Ansuzalgiz/SABR/Images/Battery.jpg

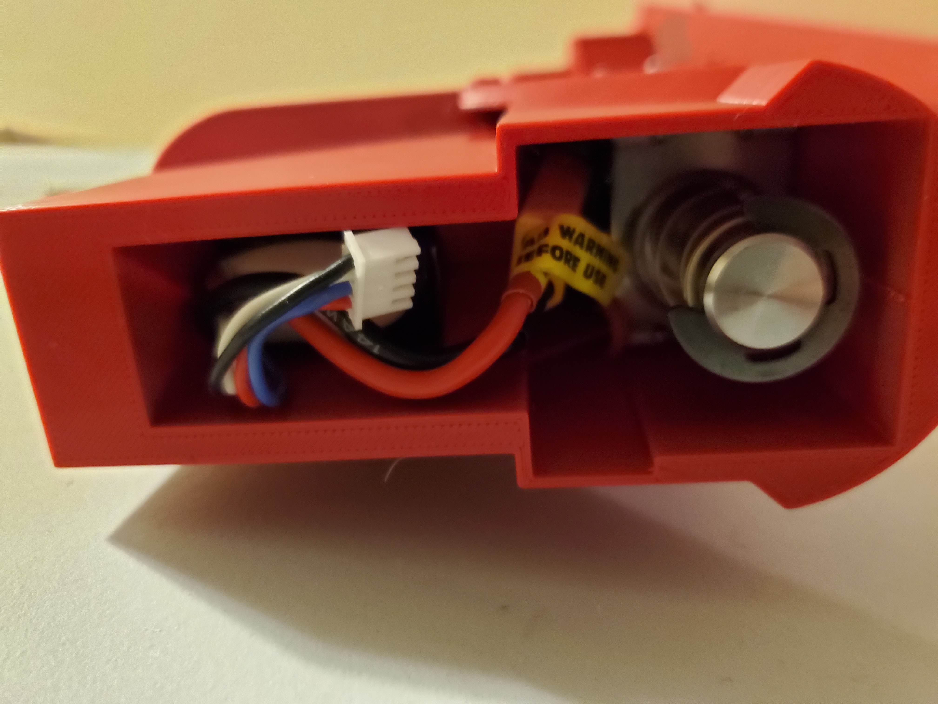
Images/Battery.jpg
