Ansuzalgiz/SABR/Images/Motors.jpg

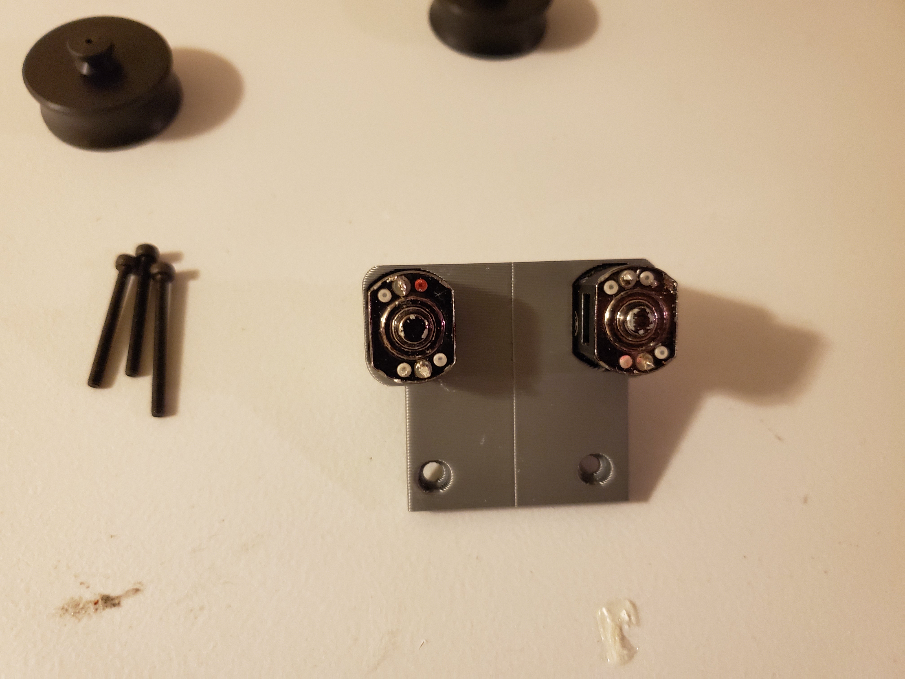
Images/Motors.jpg
