Ansuzalgiz/SABR/Images/ThreadedInserts.jpg

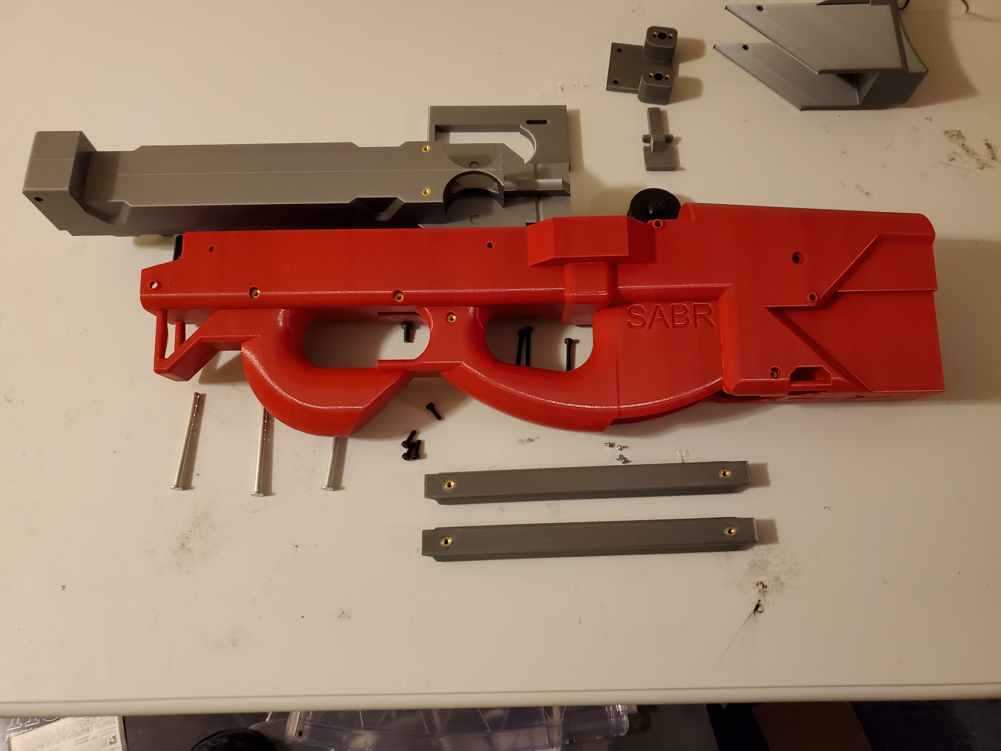
Images/ThreadedInserts.jpg
