Ansuzalgiz/SABR/STL/Barrel.stl

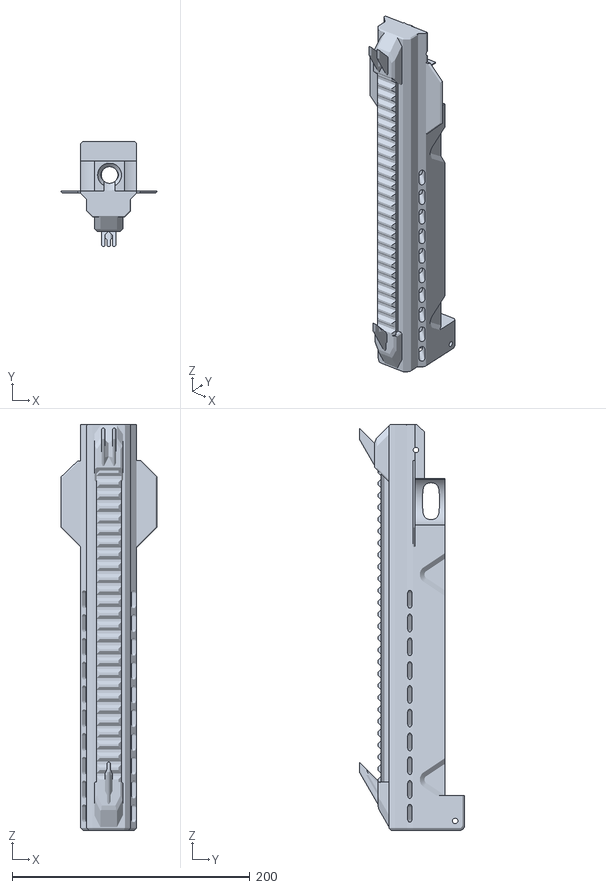
[picture p24: CAD file, 2019-04-15]
STL/Barrel.stl
80.6 x 88.7 x 341.5
