Ansuzalgiz/SABR/STL/130MotorSupport.stl

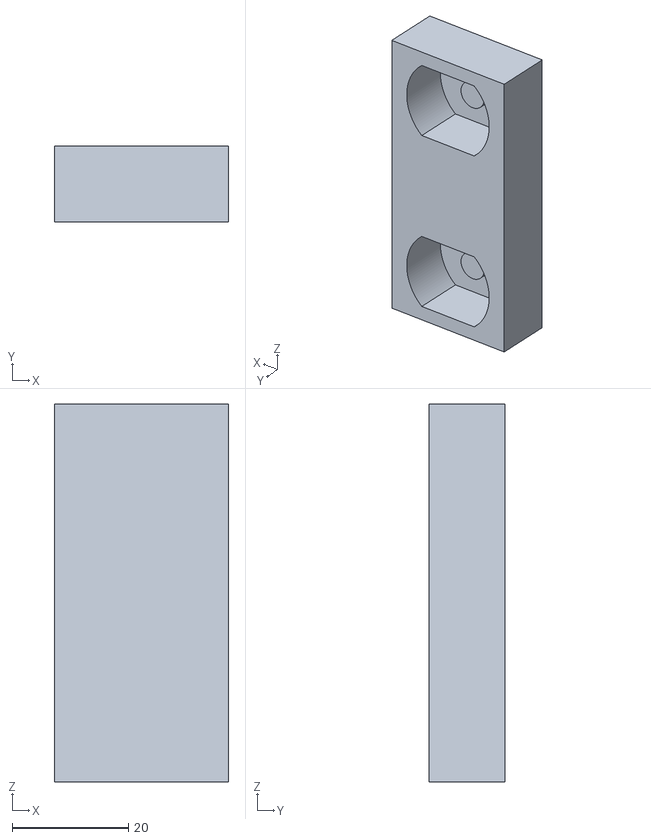
[picture p25: CAD file, 2019-04-15]
STL/130MotorSupport.stl
30.0 x 13.0 x 65.0
