Ansuzalgiz/SABR/STL/Rail.stl

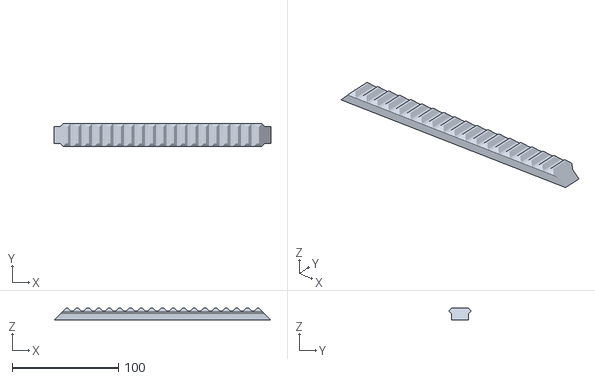
[picture p26: CAD file, 2019-04-15]
STL/Rail.stl
204.0 x 21.2 x 11.3
