Ansuzalgiz/SABR/Images/FlywheelCageInstall.jpg

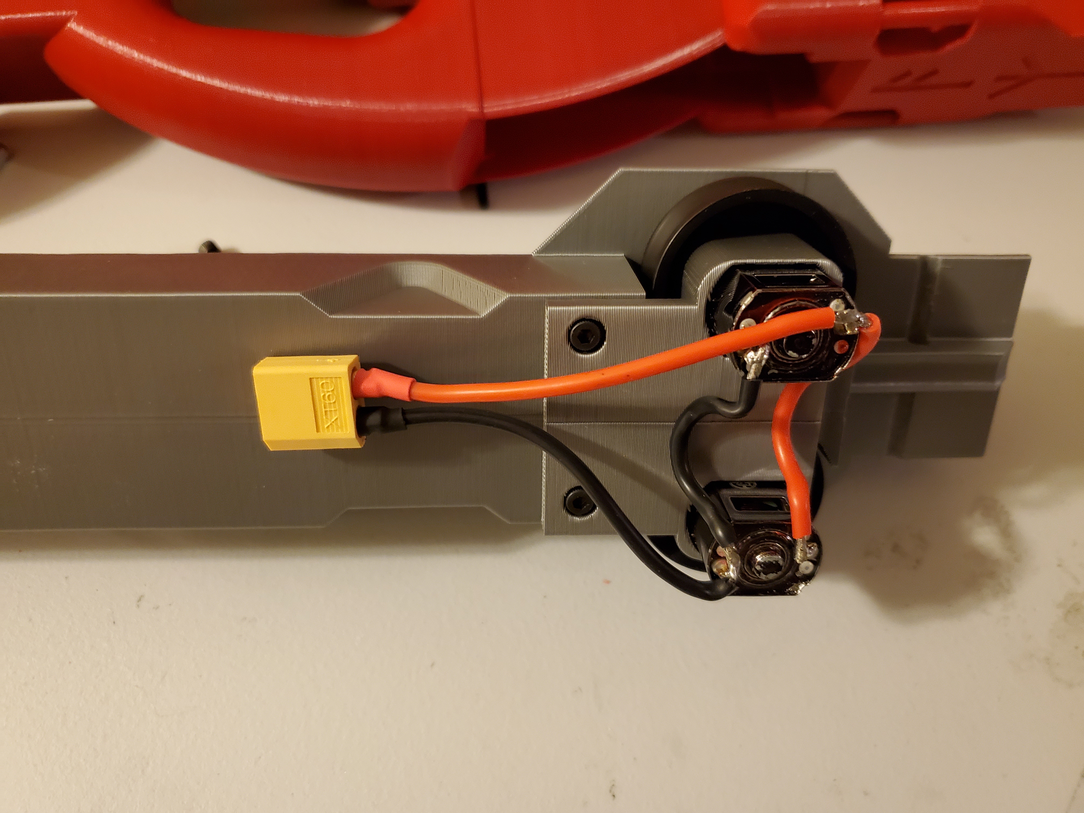
Images/FlywheelCageInstall.jpg
