Ansuzalgiz/SABR/Images/FlywheelInstallation.jpg

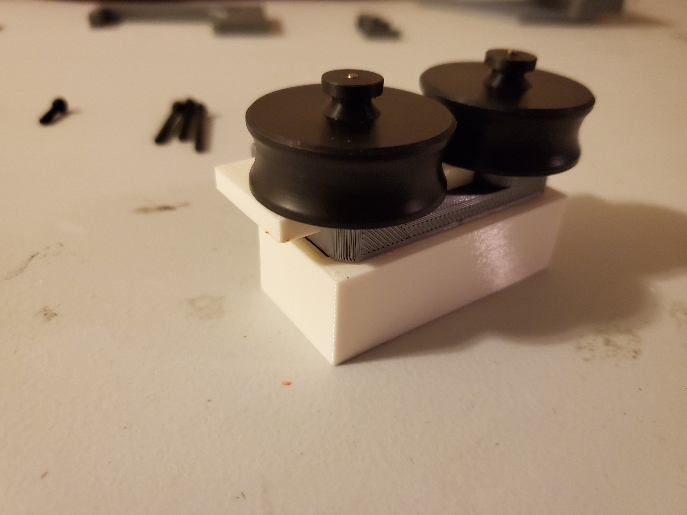
Images/FlywheelInstallation.jpg
