Ansuzalgiz/SABR/Images/MainWiring.jpg

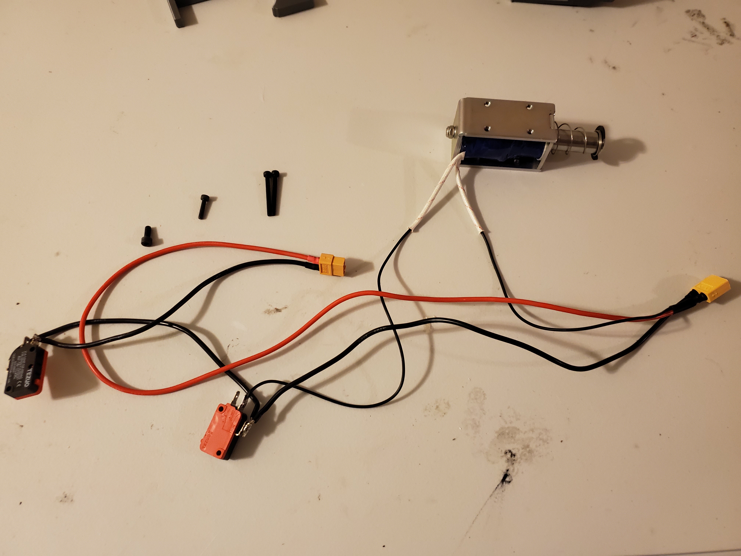
Images/MainWiring.jpg
