Ansuzalgiz/SABR/Images/MotorWiring.jpg

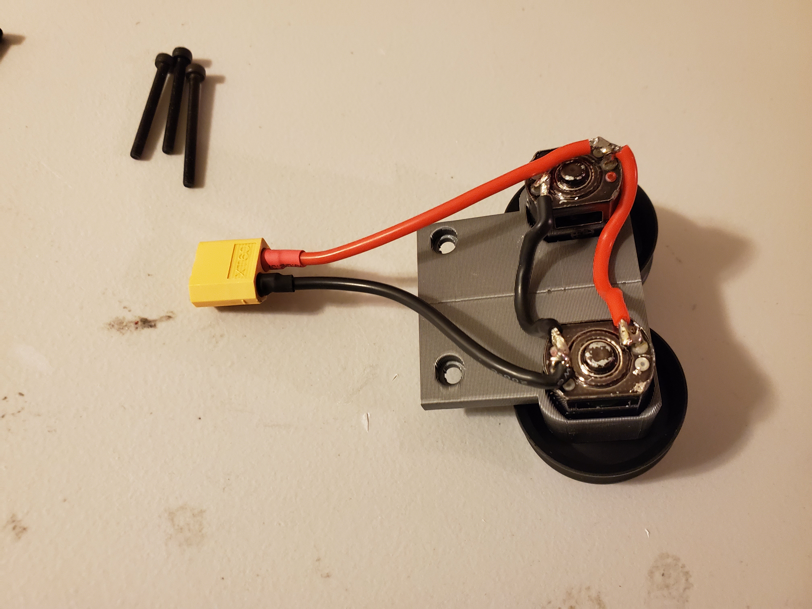
Images/MotorWiring.jpg
