Ansuzalgiz/SABR/Images/SideRailInstallation.jpg

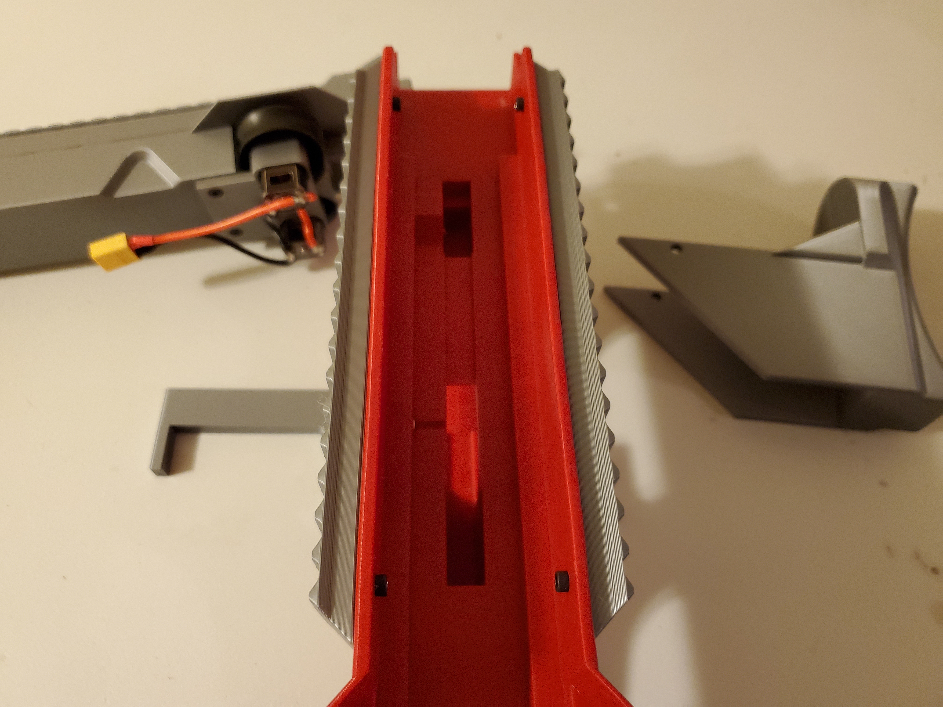
Images/SideRailInstallation.jpg
