Ansuzalgiz/SABR/Images/SwitchInstall.jpg

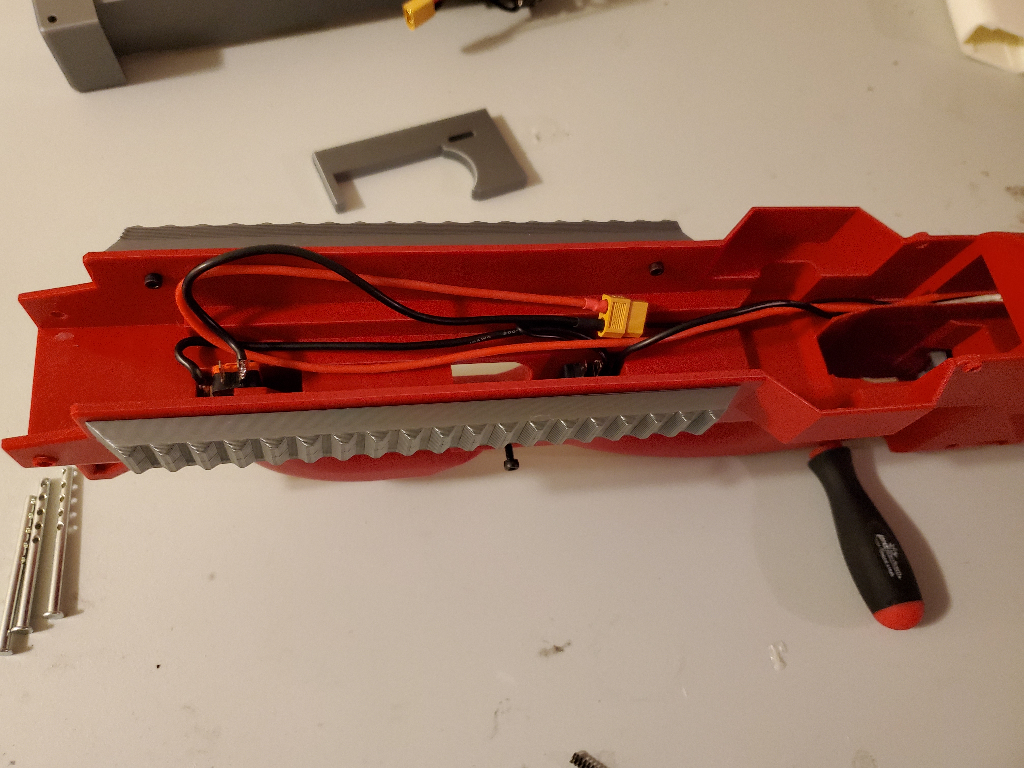
Images/SwitchInstall.jpg
