Ansuzalgiz/SABR/Images/TriggerInstall.jpg

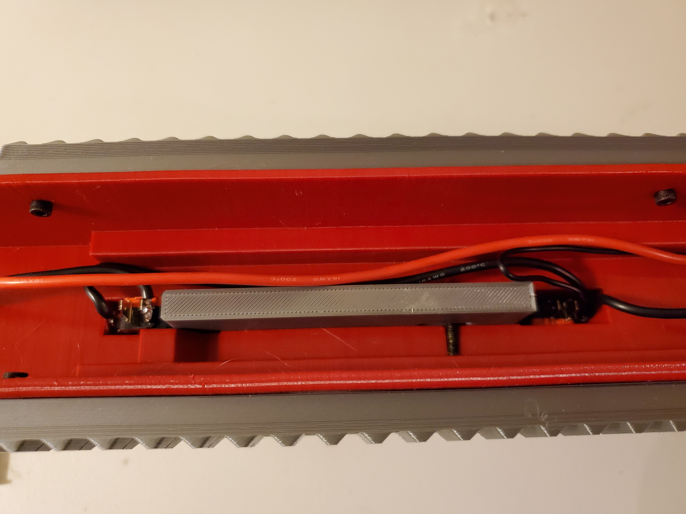
Images/TriggerInstall.jpg
