Ansuzalgiz/SABR/Images/MagReleaseInstall.jpg

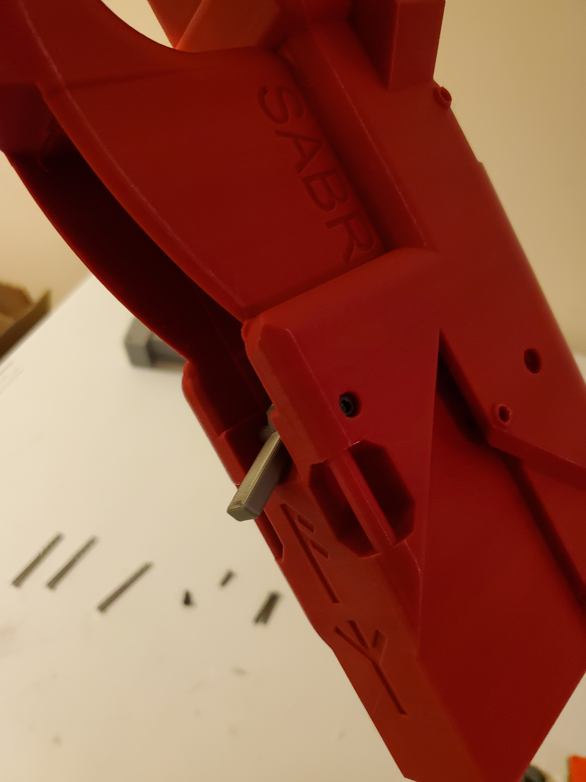
Images/MagReleaseInstall.jpg
